eldar6776/DE-020717/doc/FPC40_Connector.jpg

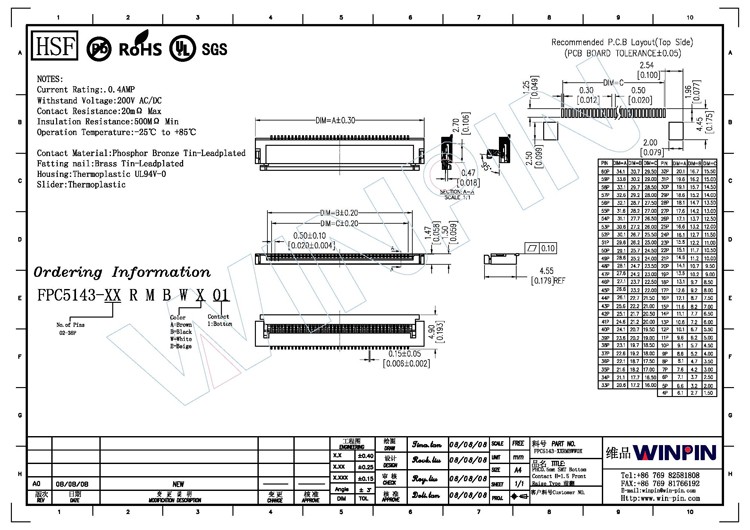
doc/FPC40_Connector.jpg
