eldar6776/DE-020717/doc/new_gui_image/background_0.bmp

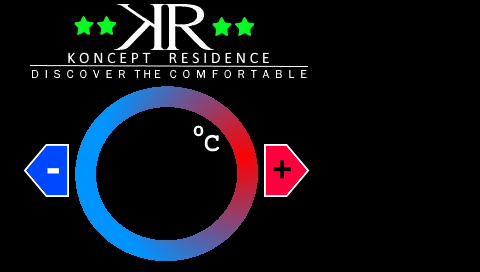
doc/new_gui_image/background_0.bmp
