eldar6776/DE-020717/doc/new_gui_image/slika2.bmp

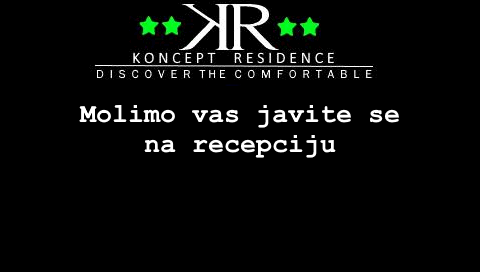
doc/new_gui_image/slika2.bmp
