eldar6776/DE-020717/doc/thermostat_gui_image/alarm_clock.png

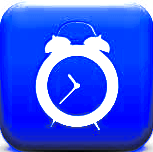
doc/thermostat_gui_image/alarm_clock.png
