eldar6776/DE-020717/doc/thermostat_gui_image/bckgnd.bmp

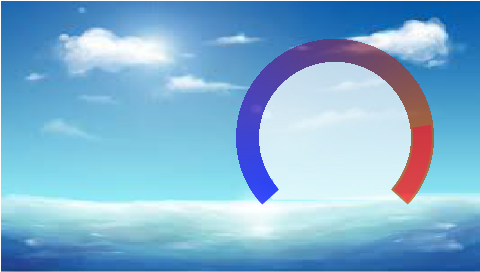
doc/thermostat_gui_image/bckgnd.bmp
