eldar6776/DE-020717/doc/thermostat_gui_image/sos.png

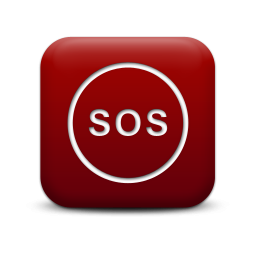
doc/thermostat_gui_image/sos.png
