eldar6776/DE-020717/doc/thermostat_gui_image/unnamed.jpg

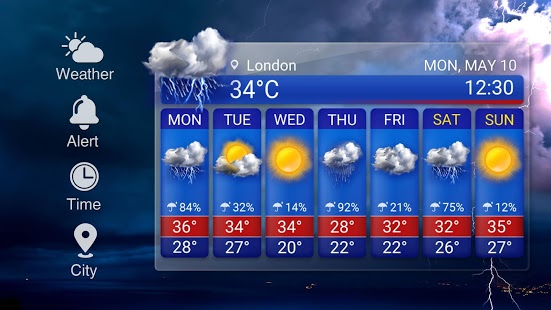
doc/thermostat_gui_image/unnamed.jpg
