eldar6776/DE-020717/doc/thermostat_gui_image/Untitled-1.png

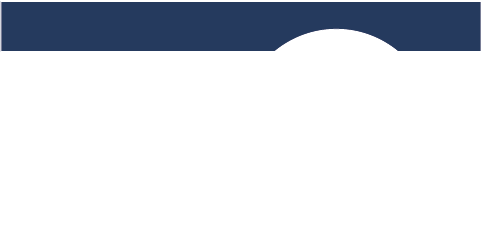
doc/thermostat_gui_image/Untitled-1.png
