eldar6776/DE-020717/STM32F746_DiscoveryThermostatGUI_Img1.JPG

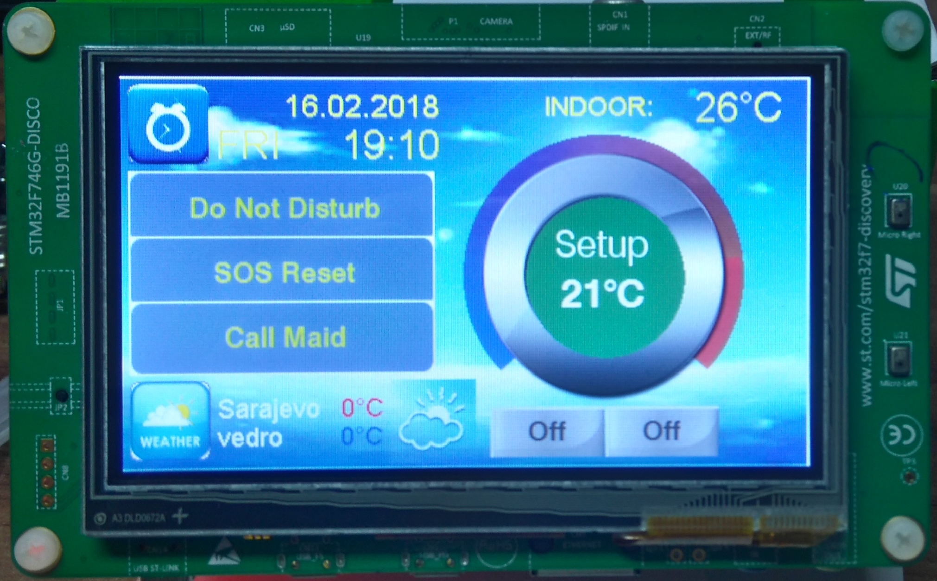
STM32F746_DiscoveryThermostatGUI_Img1.JPG
