eldar6776/DE-020717/STM32F746_DiscoveryThermostatGUI_Img2.JPG

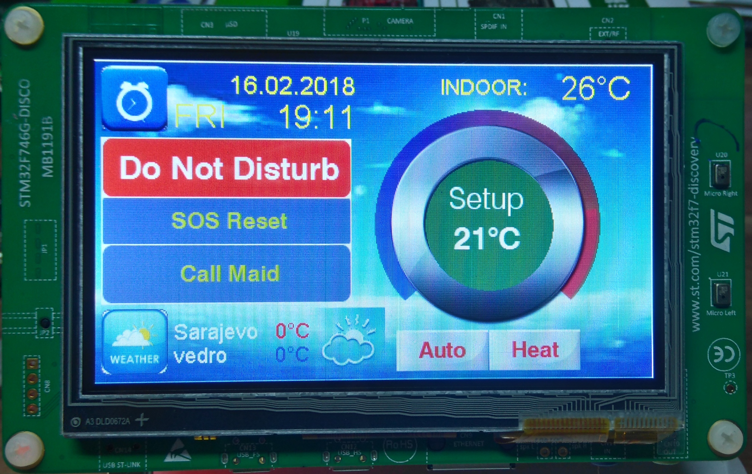
STM32F746_DiscoveryThermostatGUI_Img2.JPG
