eldar6776/DE-020717/fw/DE-170518/Inc/waveplayer.h

/**
  ******************************************************************************
  * @file    Audio/Audio_playback_and_record/Inc/waveplayer.h
  * @author  MCD Application Team
  * @brief   Header for waveplayer.c module.
  ******************************************************************************
  * @attention
  *
  * <h2><center>&copy; Copyright (c) 2016 STMicroelectronics International N.V. 
  * All rights reserved.</center></h2>
  *
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
  ******************************************************************************
  */
  
/* Define to prevent recursive inclusion -------------------------------------*/
#ifndef __WAVEPLAYER_H
#define __WAVEPLAYER_H

/* Includes ------------------------------------------------------------------*/
#include "stm32f7xx.h"


/* Exported Defines ----------------------------------------------------------*/
#define AUDIO_OUT_BUFFER_SIZE					8192
#define AUDIO_IN_PCM_BUFFER_SIZE				4*2304 /* buffer size in half-word */


/* Exported types ------------------------------------------------------------*/
typedef enum {
  AUDIO_STATE_IDLE = 0,   
  AUDIO_STATE_PLAY,
  AUDIO_STATE_STOP,
  AUDIO_STATE_ERROR  
	
}AUDIO_PLAYBACK_StateTypeDef;


typedef enum 
{
  BUFFER_OFFSET_NONE = 0,  
  BUFFER_OFFSET_HALF,  
  BUFFER_OFFSET_FULL,  
	
}BUFFER_StateTypeDef;


typedef struct 
{
  uint8_t buff[AUDIO_OUT_BUFFER_SIZE];
  BUFFER_StateTypeDef state;
  uint32_t fptr;
	
}AUDIO_OUT_BufferTypeDef;


typedef enum 
{
  BUFFER_EMPTY = 0,  
  BUFFER_FULL 
    
}WR_BUFFER_StateTypeDef;


typedef struct 
{
  uint16_t pcm_buff[AUDIO_IN_PCM_BUFFER_SIZE];
  uint32_t pcm_ptr;
  WR_BUFFER_StateTypeDef wr_state;
  uint32_t offset;  
  uint32_t fptr;
	
}AUDIO_IN_BufferTypeDef;


typedef struct	
{
	uint32_t ChunkID;
	uint32_t FileSize;
	uint32_t FileFormat;
	uint32_t SubChunk1ID;
	uint32_t SubChunk1Size;
	uint16_t AudioFormat;
	uint16_t NbrChannels; 
	uint32_t SampleRate;
	uint32_t ByteRate;
	uint16_t BlockAlign;
	uint16_t BitPerSample;
	uint32_t SubChunk2ID;  
	uint32_t SubChunk2Size;
	const uint8_t* file_name;
	
}WAVE_FormatTypeDef;


typedef enum 
{
  AUDIO_ERROR_NONE = 0,  
  AUDIO_ERROR_IO,
  AUDIO_ERROR_EOF,
  AUDIO_ERROR_INVALID_VALUE,
	
}AUDIO_ErrorTypeDef;


extern AUDIO_OUT_BufferTypeDef  BufferCtl;


/* Exported constants --------------------------------------------------------*/
/* Exported types ------------------------------------------------------------*/
/* Exported macro ------------------------------------------------------------*/
/* Exported functions ------------------------------------------------------- */
AUDIO_ErrorTypeDef AUDIO_PLAYER_Init(void);
AUDIO_ErrorTypeDef AUDIO_PLAYER_Play(const uint8_t* wave_file);
AUDIO_ErrorTypeDef AUDIO_PLAYER_Process(void);
AUDIO_ErrorTypeDef AUDIO_PLAYER_Stop(void);

#endif /* __WAVEPLAYER_H */

/************************ (C) COPYRIGHT STMicroelectronics *****END OF FILE****/
