eldar6776/DE-020717/fw/DE-170518/Inc/Resource.h

/*********************************************************************
*                SEGGER Microcontroller GmbH & Co. KG                *
*        Solutions for real time microcontroller applications        *
**********************************************************************
*                                                                    *
*        (c) 1996 - 2017  SEGGER Microcontroller GmbH & Co. KG       *
*                                                                    *
*        Internet: www.segger.com    Support:  support@segger.com    *
*                                                                    *
**********************************************************************

** emWin V5.42 - Graphical user interface for embedded applications **
emWin is protected by international copyright laws.   Knowledge of the
source code may not be used to write a similar product.  This file may
only  be used  in accordance  with  a license  and should  not be  re-
distributed in any way. We appreciate your understanding and fairness.
----------------------------------------------------------------------
File        : Resource.h
Content     : Main resource header file of weather forecast demo
---------------------------END-OF-HEADER------------------------------
*/

#ifndef RESOURCE_H
#define RESOURCE_H

#include "GUI.h"
//
//	Sound
//

//
// 	Font
//

//
// 	Image
//
extern GUI_CONST_STORAGE GUI_BITMAP bm_btn_ok;
extern GUI_CONST_STORAGE GUI_BITMAP bm_btn_open_door;
extern GUI_CONST_STORAGE GUI_BITMAP bm_btn_dnd_0;
extern GUI_CONST_STORAGE GUI_BITMAP bm_btn_dnd_1;
extern GUI_CONST_STORAGE GUI_BITMAP bm_btn_maid_0;
extern GUI_CONST_STORAGE GUI_BITMAP bm_btn_maid_1;
extern GUI_CONST_STORAGE GUI_BITMAP bm_btn_rst_sos_0;
extern GUI_CONST_STORAGE GUI_BITMAP bm_btn_rst_sos_1;
extern GUI_CONST_STORAGE GUI_BITMAP bm_display_0;
extern GUI_CONST_STORAGE GUI_BITMAP bm_display_1;
extern GUI_CONST_STORAGE GUI_BITMAP bm_display_2;
extern GUI_CONST_STORAGE GUI_BITMAP bm_number_0;
extern GUI_CONST_STORAGE GUI_BITMAP bm_number_1;
extern GUI_CONST_STORAGE GUI_BITMAP bm_number_2;
extern GUI_CONST_STORAGE GUI_BITMAP bm_number_3;
extern GUI_CONST_STORAGE GUI_BITMAP bm_number_4;
extern GUI_CONST_STORAGE GUI_BITMAP bm_number_5;
extern GUI_CONST_STORAGE GUI_BITMAP bm_number_6;
extern GUI_CONST_STORAGE GUI_BITMAP bm_number_7;
extern GUI_CONST_STORAGE GUI_BITMAP bm_number_8;
extern GUI_CONST_STORAGE GUI_BITMAP bm_number_9;
//
//	Animation
//
#endif // RESOURCE_H

/*************************** End of file ****************************/
