eldar6776/DE-020717/fw/STM32F746_DiscoveryDemo/Inc/thermostat.h

/**
 ******************************************************************************
 * File Name          : thermostat.h
 * Date               : 22/02/2018 07:03:00
 * Description        : temperature controller header
 ******************************************************************************
 */
 
 
 /* Define to prevent recursive inclusion -------------------------------------*/
#ifndef TEMP_CTRL_H
#define TEMP_CTRL_H     			211		// version


/* Includes ------------------------------------------------------------------*/
#include "stm32f7xx.h"


/* Exported Type  ------------------------------------------------------------*/
typedef struct
{ 	
	uint8_t valve;						// pipe valve state
	uint8_t fan_mode;					// fan control: auto/low/medium/high
	uint8_t fan_speed;					// fan speed: off/low/med/high
	uint8_t ctrl_mode;					// controler mode: off/cool/heat
	uint16_t actual_temperature;		// measured temperature	
	uint16_t set_temperature;			// set point temperature
	uint8_t	set_temperature_diff;		// set point tempearture difference
	uint8_t	fan_low_speed_band;			// middle to low fan speed change in auto mode 
	uint8_t	fan_middle_speed_band;		// high to middle fan speed change in auto mode
	uint8_t fan_speed_diff;				// fan speed change value differenc in auto mode
	
}THERMOSTAT_TypeDef;

extern THERMOSTAT_TypeDef Thermostat_1;


/* Exported Define  ----------------------------------------------------------*/
#define THERMOSTAT_CONTROL_MODE_OFF			0
#define THERMOSTAT_CONTROL_MODE_COOLING		1
#define THERMOSTAT_CONTROL_MODE_HEATING		2
#define THERMOSTAT_MAX_TEMPERATURE			320		// 32,0°C max. thermostat setup temperature
#define THERMOSTAT_MIN_TEMPERATURE			140		// 14,0°C min. thermostat setup temperature
#define THERMOSTAT_FAN_MODE_AUTO			0
#define THERMOSTAT_FAN_MODE_LOW				1
#define THERMOSTAT_FAN_MODE_MIDDLE			2
#define THERMOSTAT_FAN_MODE_HIGH			3

/* Exported Variable   -------------------------------------------------------*/
extern __IO uint32_t thermostat_timer;
extern __IO uint32_t thermostat_fan_timer;
extern __IO uint32_t thermostat_valve_timer;
extern uint32_t thermostat_flags;


/* Exported Macro ------------------------------------------------------------*/
#define THERMOSTAT_StartTimer(TIME)			(thermostat_timer = TIME)
#define THERMOSTAT_StopTimer()				(thermostat_timer = 0)
#define IsTHERMOSTAT_TimerExpired()			(thermostat_timer == 0)
#define THERMOSTAT_StartFanTimer(TIME)		(thermostat_fan_timer = TIME)
#define THERMOSTAT_StopFanTimer()			(thermostat_fan_timer = 0)
#define IsTHERMOSTAT_FanTimerExpired()		(thermostat_fan_timer == 0)
#define THERMOSTAT_StartValveTimer(TIME)	(thermostat_valve_timer = TIME)
#define THERMOSTAT_StopValveTimer()			(thermostat_valve_timer = 0)
#define IsTHERMOSTAT_ValveTimerExpired()	(thermostat_valve_timer == 0)
#define THERMOSTAT_TemperatureUpdateSet()	(thermostat_flags |= 0x00000001)
#define THERMOSTAT_TemperatureUpdateReset()	(thermostat_flags &= 0xfffffffe)
#define IsTHERMOSTAT_TemperatureUpdated()	(thermostat_flags & 0x00000001)


/* Exported Function  ------------------------------------------------------- */
void THERMOSTAT_Init(void);
void THERMOSTAT_Service(void);


#endif
/******************************   END OF FILE  ********************************/
